DmitriiTrifonov/skladen/export/switch/finger0.5/mk3-switch-shuttle-finger0.5-proud3.0.stl

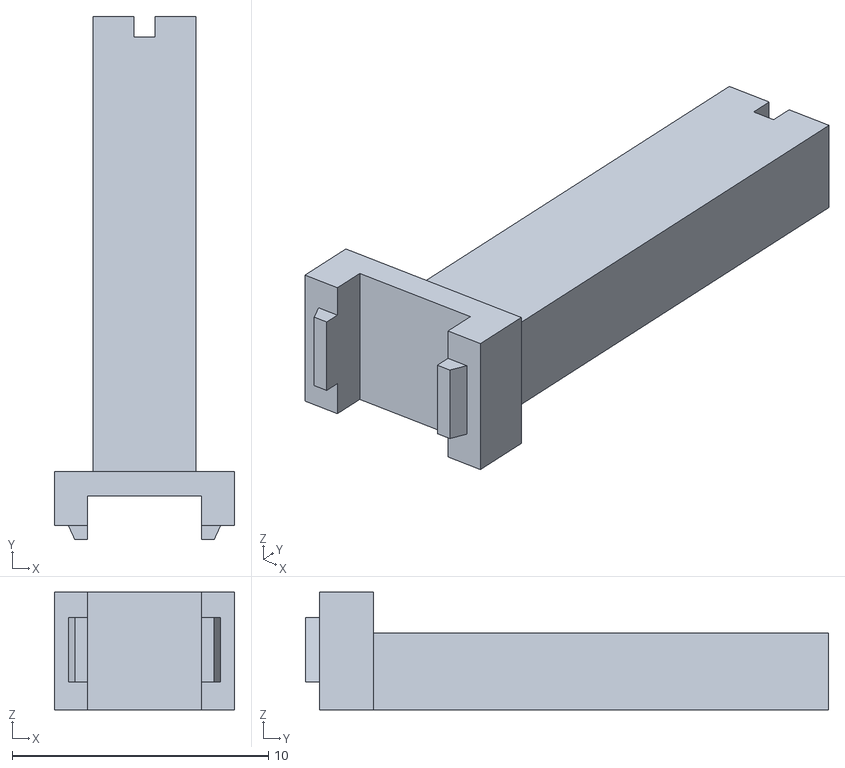
[picture p15: CAD file, 2026-09-30]
export/switch/finger0.5/mk3-switch-shuttle-finger0.5-proud3.0.stl
7.04 x 20.4 x 4.60
