DmitriiTrifonov/skladen/export/switch/finger1.5/mk3-switch-shuttle-finger1.5-proud3.0.stl

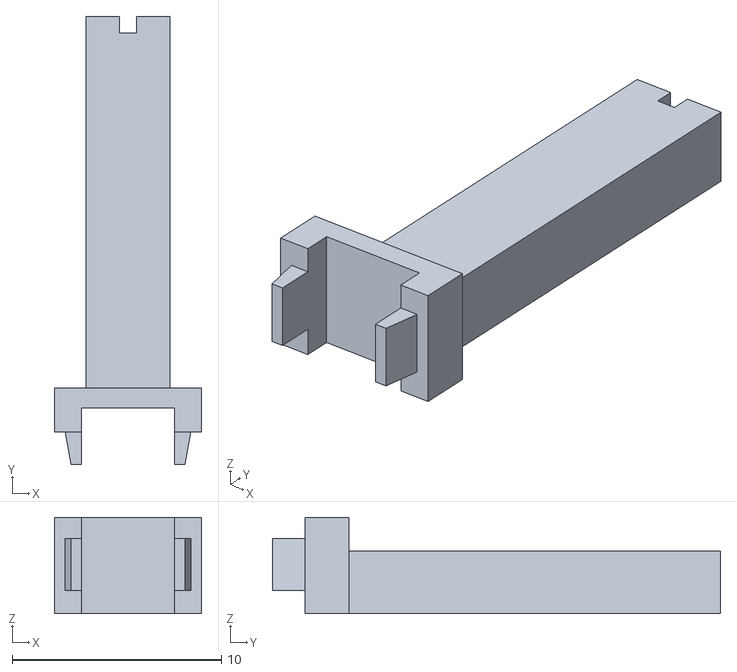
[picture p16: CAD file, 2026-09-30]
export/switch/finger1.5/mk3-switch-shuttle-finger1.5-proud3.0.stl
7.04 x 21.4 x 4.60
